nunojay/PrintableSDCardWallets/SDCardWallet3x2.scad

include <SDCardWalletLib.scad>;

//// Overwrite configuration variables from SDCardWalletLib:

cHoldersCfg = [ [0, 0],
                [0, 0],
                [0, 0],
              ];
cFingerOpenWidth = 0.45;    // %/100 of X axis box len
cLockDistFromSide = 14;

//// Build it!
Wallet();
